syarusinsky/BITBA555/BITBA555_Completed/Hardware/BITBA555_tutorial5_pcb.png

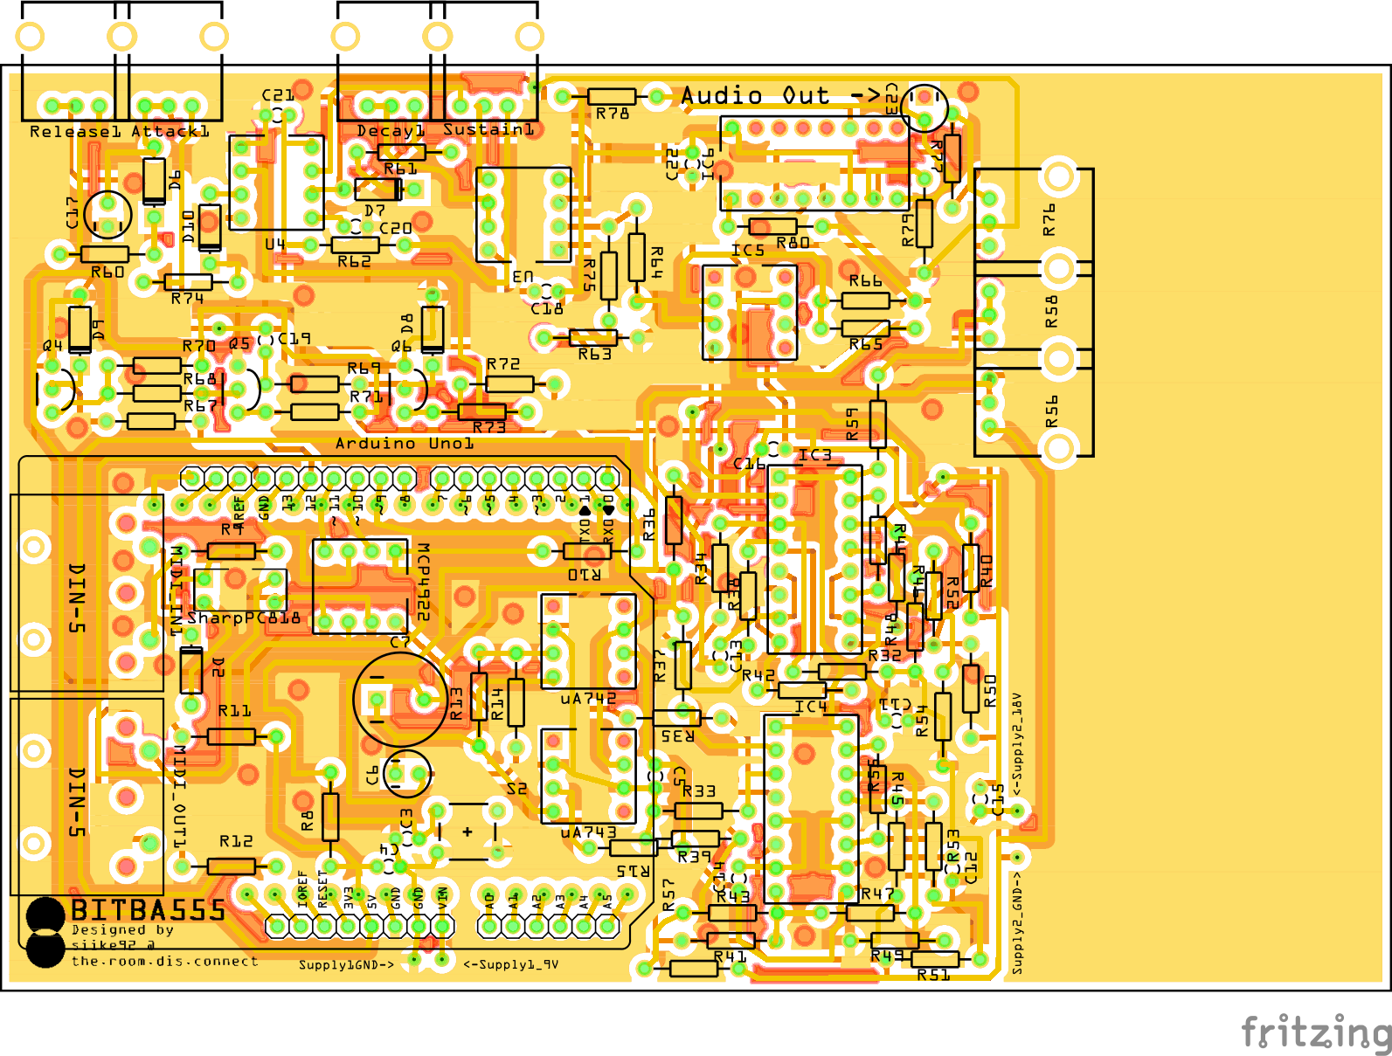
BITBA555_Completed/Hardware/BITBA555_tutorial5_pcb.png
