syarusinsky/BITBA555/BITBA555_tutorial4/Hardware/BITBA555_tutorial3_breadboard_layout.png

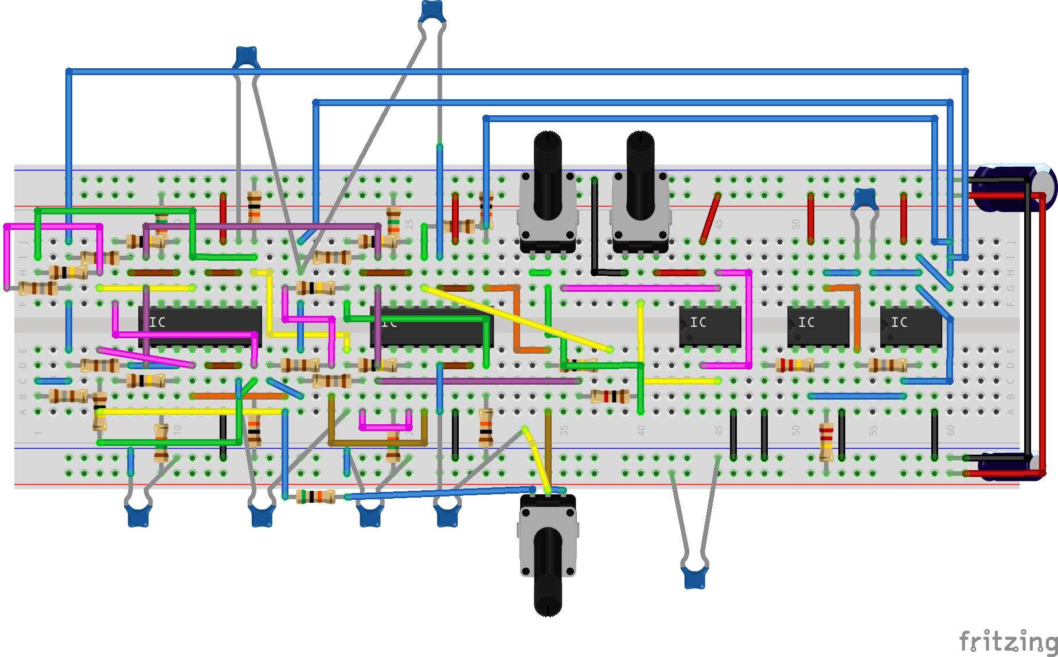
BITBA555_tutorial4/Hardware/BITBA555_tutorial3_breadboard_layout.png
