syarusinsky/BITBA555/BITBA555_Completed/Hardware/BITBA555_tutorial5_etchable_pdf/BITBA555_tutorial5_etch_silk_bottom.pdf

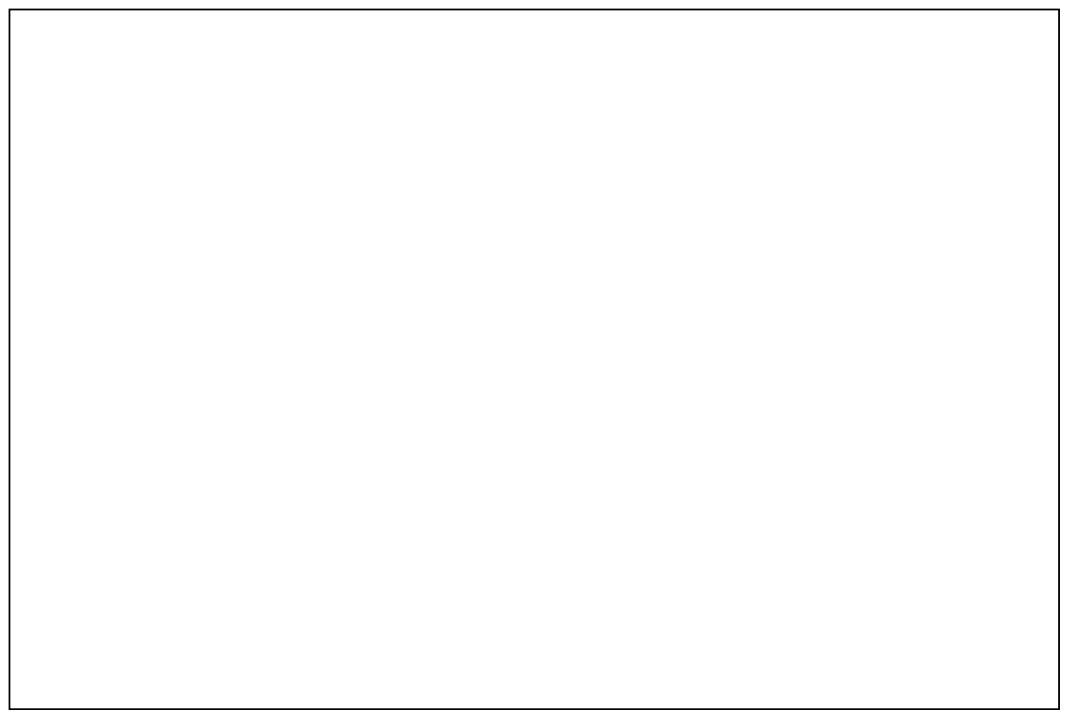
[picture p26: page 1]
