syarusinsky/BITBA555/BITBA555_Completed/Hardware/BITBA555_tutorial5_etchable_pdf/BITBA555_tutorial5_etch_silk_bottom_mirror.pdf

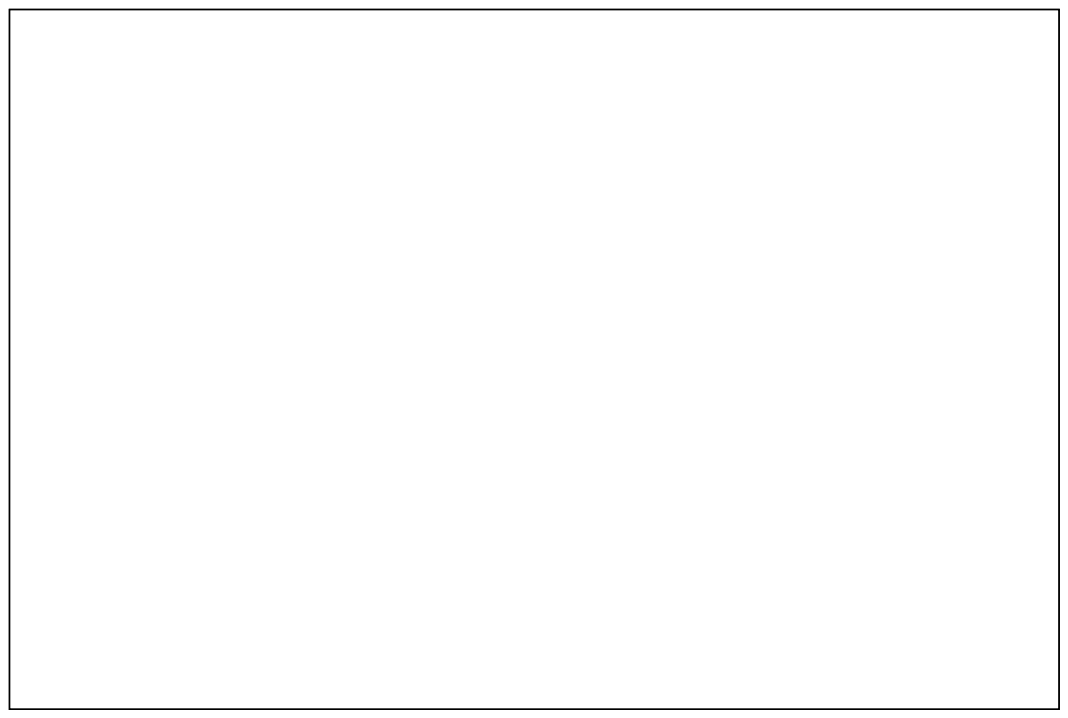
[picture p27: page 1]
