syarusinsky/BITBA555/BITBA555_Completed/Hardware/BITBA555_tutorial5_etchable_pdf/BITBA555_tutorial5_etch_silk_top.pdf

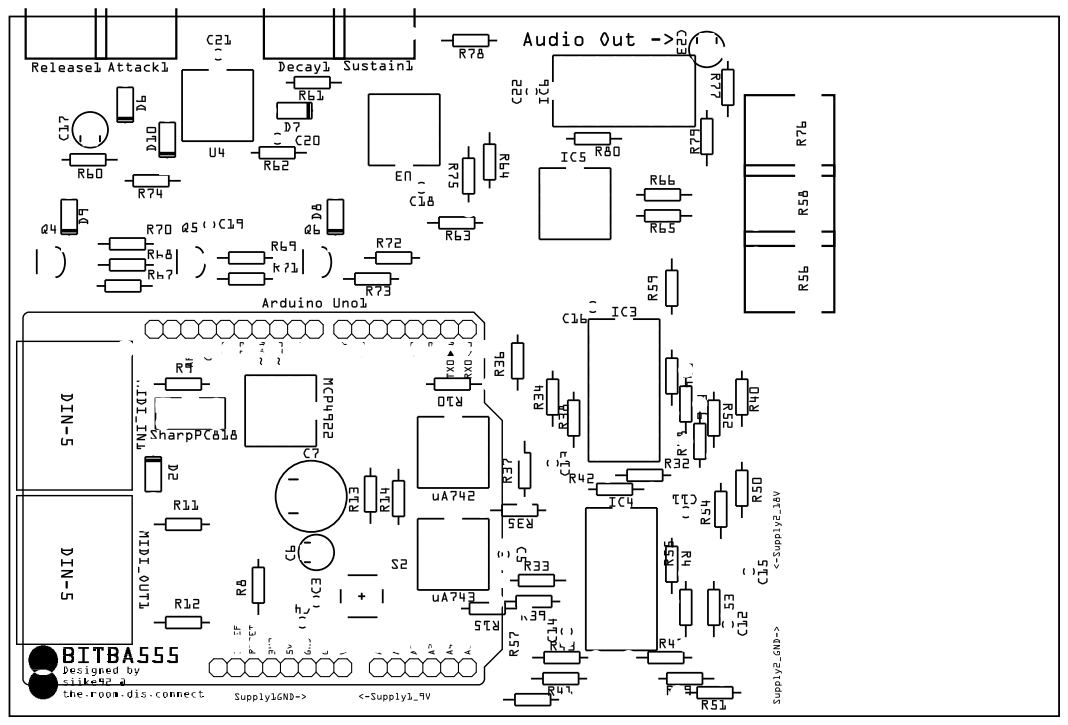
[picture p28: page 1]
