syarusinsky/BITBA555/BITBA555_Completed/Hardware/BITBA555_tutorial5_etchable_pdf/BITBA555_tutorial5_etch_silk_top_mirror.pdf

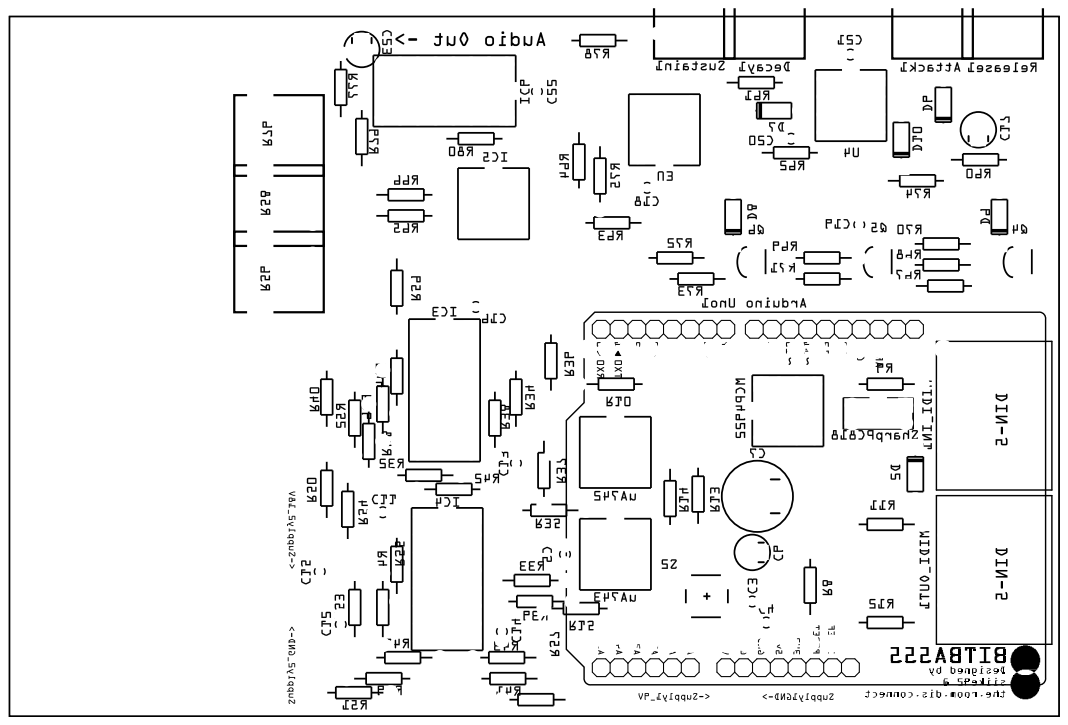
[picture p29: page 1]
