syarusinsky/BITBA555/BITBA555_Completed/Simulation/EnvelopeGenerator.asc

Attack: res; 1k
C1: cap; 0.1µ
C2: cap; 0.1µ
C3: cap; 3.3µF
C4: cap; 0.1µ
C5: cap; 0.1µ
C6: cap; 0.1µ
D1: diode; 1N4148
D2: diode; 1N4148
D3: diode; 1N4148
D4: diode; 1N4148
D5: diode; 1N4148
Decay: res; 10k
Q1: npn; 2N3904
Q2: npn; 2N3904
Q3: npn; 2N3904
R1: res; 10k
R2: res; 5.6k
R3: res; 10k
R4: res; 5.6k
R5: res; 10k
R6: res; 1k
R7: res; 5.6k
R8: res; 180
R9: res; 180
R10: res; 180
R11: res; 10k
R12: res; 8k
R13: res; 5.6k
Release: res; 10
Sustain1: res; 300k
Sustain2: res; 200k
U1: NE555
U2: opamp2; LM358
U3: opamp2; LM358
V1: voltage; 5
V2: voltage; PULSE(0 5 0.2 0 0 0.5 1 1)
V3: voltage; 9
V4: voltage; -9
Named nets: 0, 5V, 9V, -9V\, -9V, DIS
.tran 0 1 0
.inc LM358.lib
