syarusinsky/BITBA555/BITBA555_Completed/Simulation/EnvelopeGeneratorRanger.asc

R1: res; 20k
R2: res; 10k
U1: uA741
V1: voltage; 0.3
V2: voltage; 9V
V3: voltage; -9
Named nets: 0, 9V, -9V
.tran 0 1 0
