syarusinsky/BITBA555/BITBA555_Completed/Simulation/LM13700VCA.asc

C1: cap; 47µF
R2: res; 500
R3: res; 500
R4: res; 30k
R5: res; 220k
R6: res; 30k
R7: res; 5k
U1: LM13700
V1: voltage; 9
V2: voltage; -9
V3: voltage; PULSE(-2 2 0 0 0 0.02 0.04 30)
V4: voltage; 9
Named nets: 9V, -9V, 0
.tran 0 1 0
.lib lm13700.sub
