syarusinsky/BITBA555/BITBA555_Completed/Simulation/LM137004PoleFilterWithResonance.asc

C1: cap; 300pF
C2: cap; 300pF
C3: cap; 300pF
C4: cap; 300pF
R1: res; 180
R2: res; 100k
R3: res; 180
R4: res; 10k
R5: res; 10k
R6: res; 100k
R7: res; 100k
R8: res; 180
R9: res; 180
R10: res; 100k
R11: res; 1k
R12: res; 15k
R13: res; 15k
R14: res; 180
R15: res; 100k
R16: res; 180
R17: res; 10k
R18: res; 10k
R19: res; 100k
R20: res; 100k
R21: res; 180
R22: res; 180
R23: res; 100k
R24: res; 15k
R25: res; 15k
R26: res; 50k
R27: res; 1Meg
R28: res; 180
U1: LM13700
U2: LM13700
U3: LM13700
U4: LM13700
V1: voltage; 9
V2: voltage; -9
V3: voltage; 6
V4: voltage; ""; AC 5
Named nets: 0, +9V, -9V
.lib lm13700.sub
.ac dec 20 20 20000
Cutoff
Resonance
