syarusinsky/BITBA555/BITBA555_Completed/Simulation/LM138002PolePulseTransient.asc

C1: cap; 100p
C2: cap; 200p
R1: res; 100k
R2: res; 180
R3: res; 180
R4: res; 10k
R5: res; 100k
R6: res; 180
R7: res; 100k
R8: res; 180
R9: res; 10k
R10: res; 15k
R11: res; 10k
R12: res; 10k
U1: LM13700
U2: LM13700
V1: voltage; 9
V2: voltage; -9
V3: voltage; 0
V4: voltage; PULSE(5 0 .2 0 0 .005 .01 10)
Named nets: 0, 9V, -9V
.lib lm13700.sub
.tran 0 1.5 0
