syarusinsky/BITBA555/BITBA555_Completed/Simulation/PowerSupply.asc

C1: cap; 10µ
C2: cap; 100µ
C3: cap; 10p
R1: res; 220k
R2: res; 220k
R3: res; 180
U1: uA741
U2: uA741
V1: voltage; 18V
Named nets: 0, VGND, -9V, 9V
.tran 0 1 0
