syarusinsky/BITBA555/BITBA555_Completed/Simulation/SimpleRCLowPassFilter.asc

C1: cap; 100n
R1: res; 10k
V1: voltage; PULSE(0 5 .2 0.0 0.0 .01 .02 5)
Named nets: 0
.tran 0 1.2 0
